bitfieldlabs/aggi/afterglow_gi_nano_ps/afterglow_gi_nano_ps.jpg

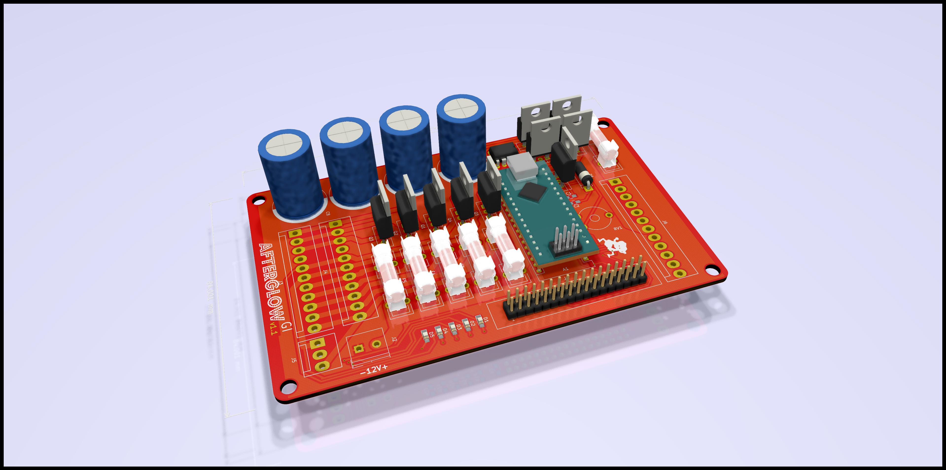
afterglow_gi_nano_ps/afterglow_gi_nano_ps.jpg
