bitfieldlabs/aggi/doc/images/cable_extension_11pin.jpg

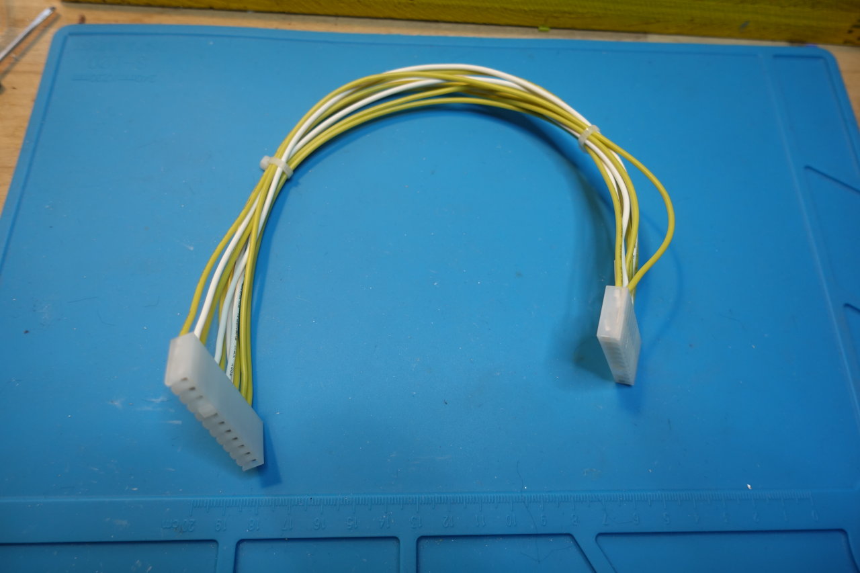
doc/images/cable_extension_11pin.jpg
