bitfieldlabs/aggi/doc/images/power_supply_12V_mounted.jpg

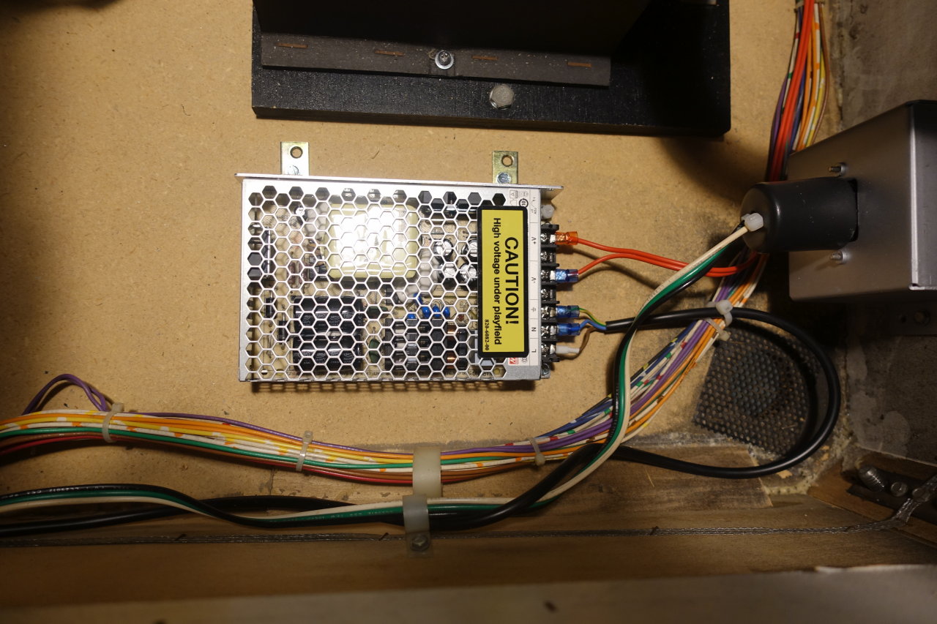
doc/images/power_supply_12V_mounted.jpg
