bitfieldlabs/aggi/scopes/creature_orig_gi_1_brightness_4_at_triac.png

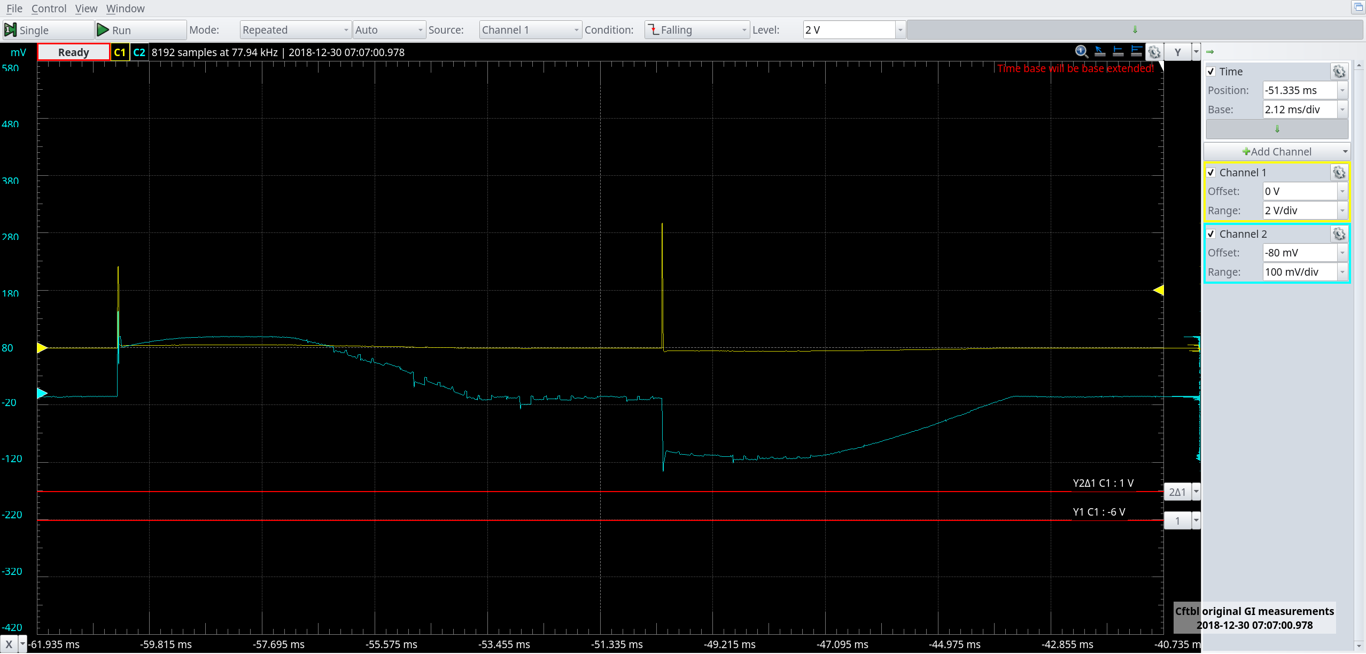
scopes/creature_orig_gi_1_brightness_4_at_triac.png
