bitfieldlabs/aggi/scopes/creature_orig_gi__zero_crossing_vs_T0_brightness_4_max.png

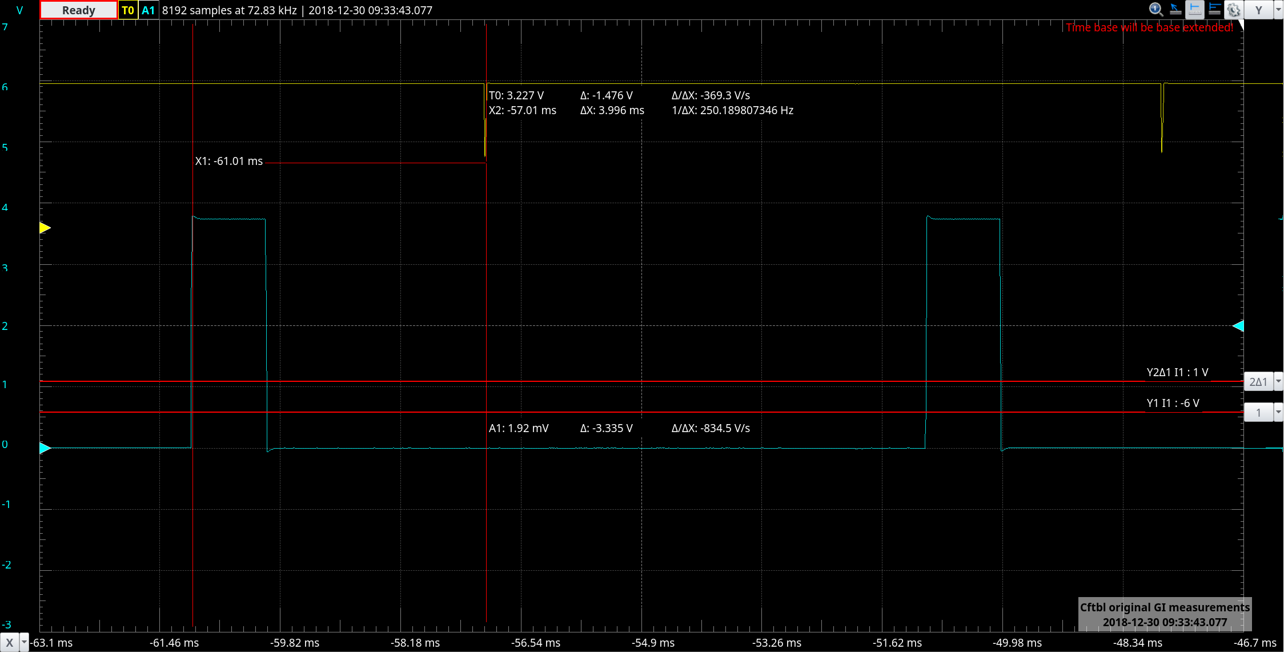
scopes/creature_orig_gi__zero_crossing_vs_T0_brightness_4_max.png
