bitfieldlabs/aggi/scopes/creature_orig_gi__zero_crossing_vs_T0_brightness_7.png

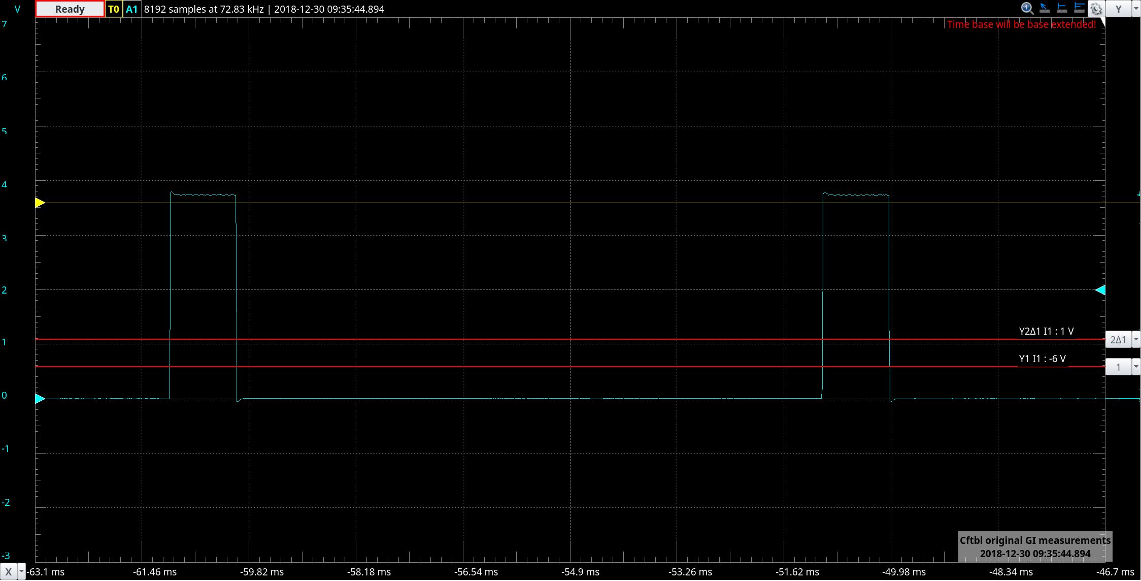
scopes/creature_orig_gi__zero_crossing_vs_T0_brightness_7.png
