bitfieldlabs/aggi/doc/images/pcb_v10_q3fix.jpg

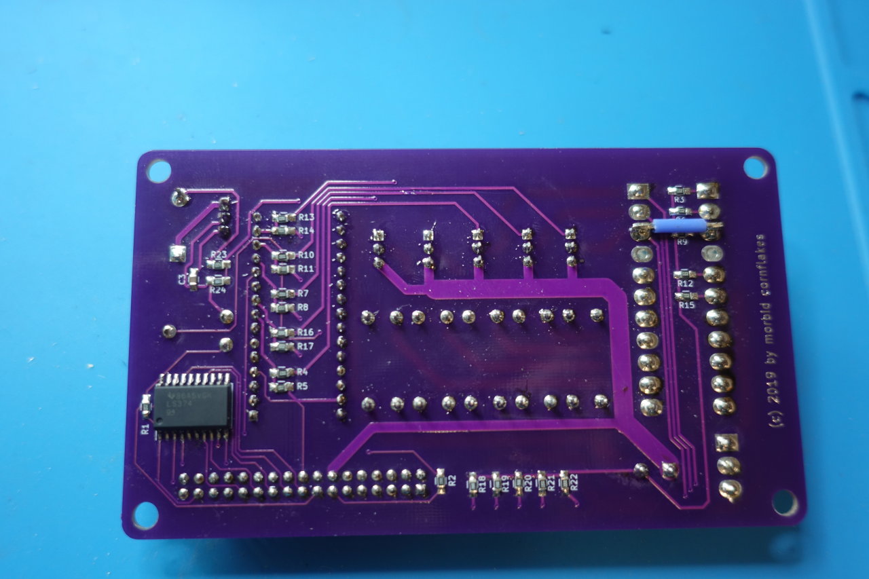
doc/images/pcb_v10_q3fix.jpg
